research-group-moven/aqara-camera-ifttt-interface/hardware/board/aqara-camera-ifttt-interface.kicad_sch

## KiCad design hardware/board/aqara-camera-ifttt-interface.kicad_sch (2026-06-12)

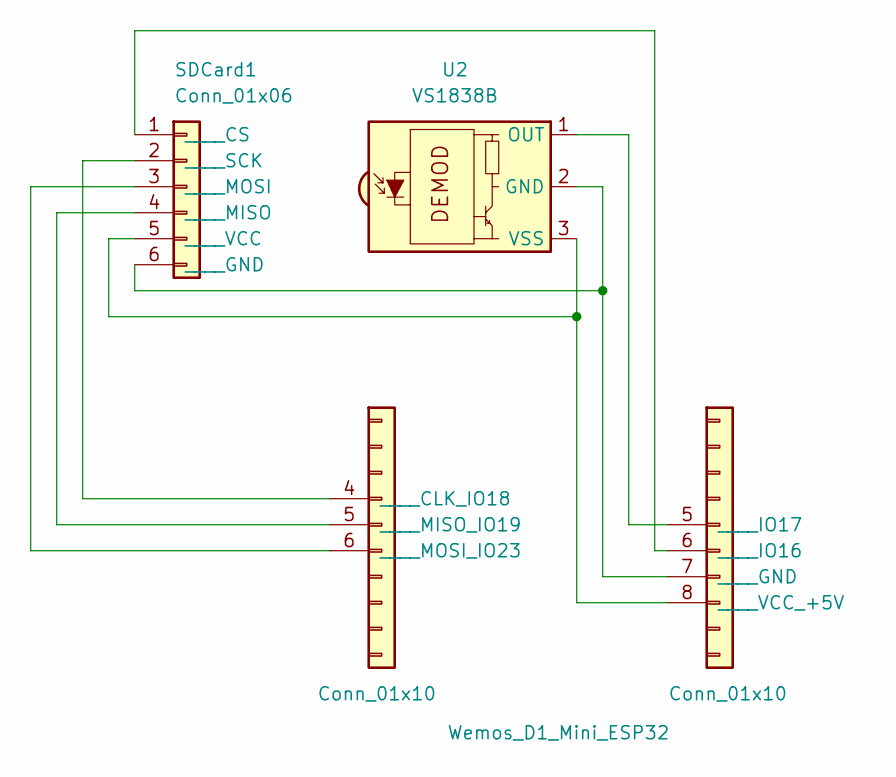
[picture p5: schematic aqara-camera-ifttt-interface.kicad_sch]

Parts:
J1: Conn_01x10; PinSocket_1x10_P2.54mm_Vertical
SDCard1: Conn_01x06; PinSocket_1x06_P2.54mm_Vertical
U2: VS1838B; Vishay_MINICAST-3Pin
Wemos_D1_Mini_ESP32: Conn_01x10; PinSocket_1x10_P2.54mm_Vertical

Connections:
unnamed: J1.4 (____CLK_IO18), SDCard1.2 (____SCK)
unnamed: J1.5 (____MISO_IO19), SDCard1.4 (____MISO)
unnamed: J1.6 (____MOSI_IO23), SDCard1.3 (____MOSI)
unnamed: SDCard1.1 (____CS), Wemos_D1_Mini_ESP32.6 (____IO16)
unnamed: SDCard1.5 (____VCC), U2.3 (VSS), Wemos_D1_Mini_ESP32.8 (____VCC_+5V)
unnamed: SDCard1.6 (____GND), U2.2 (GND), Wemos_D1_Mini_ESP32.7 (____GND)
unnamed: U2.1 (OUT), Wemos_D1_Mini_ESP32.5 (____IO17)
